digunderground/secura/STL/Secura-stand/Secura Stand-filled.png

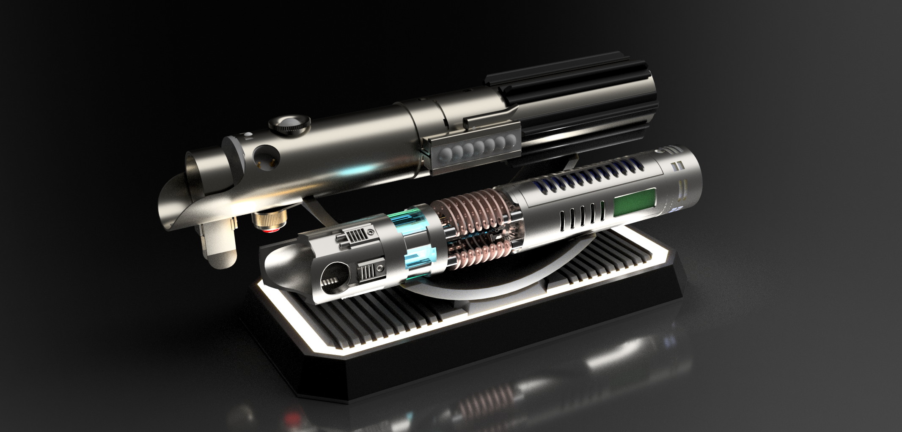
STL/Secura-stand/Secura Stand-filled.png
