digunderground/secura/Extras/proffieTester/STL/wiring_tester_v5_test-bottom.stl

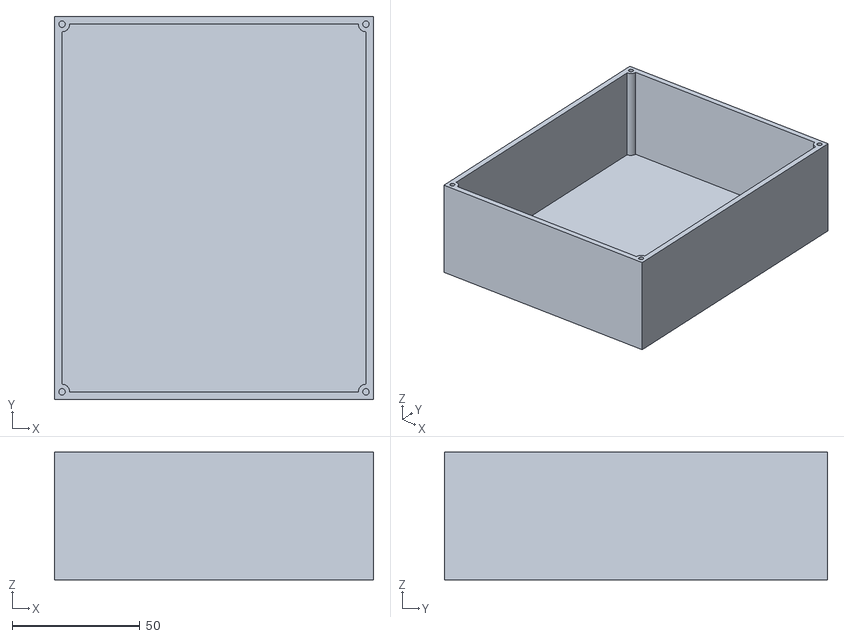
[picture p25: CAD file, 2025-04-27]
Extras/proffieTester/STL/wiring_tester_v5_test-bottom.stl
125.0 x 150.0 x 50.0
