digunderground/secura/MODS/Digunderground/experimental/Secura-chassis/Secura-CH-EXP-21700-Chassis.step

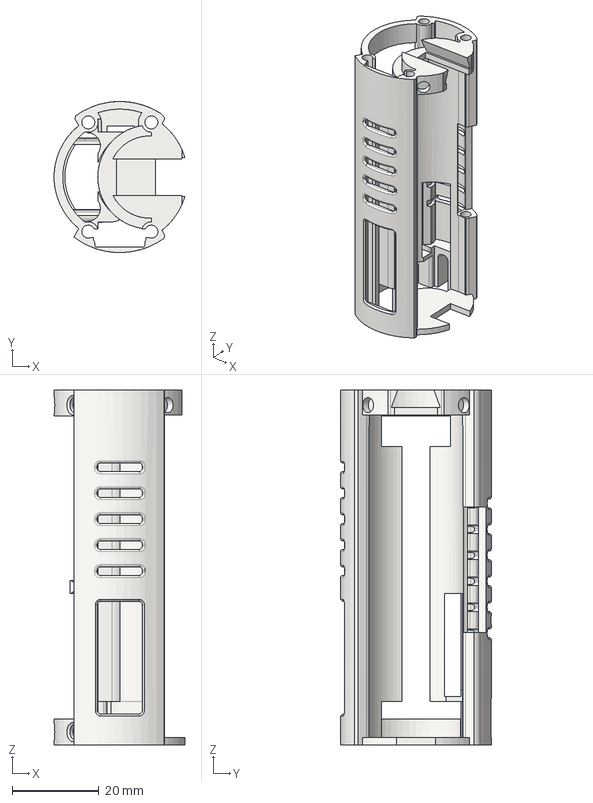
[picture p26: CAD file, 2025-04-13]
MODS/Digunderground/experimental/Secura-chassis/Secura-CH-EXP-21700-Chassis.step
30.2 x 34.9 x 82.0 mm
