digunderground/secura/STL/Secura-chassis/CH-chassis.stl

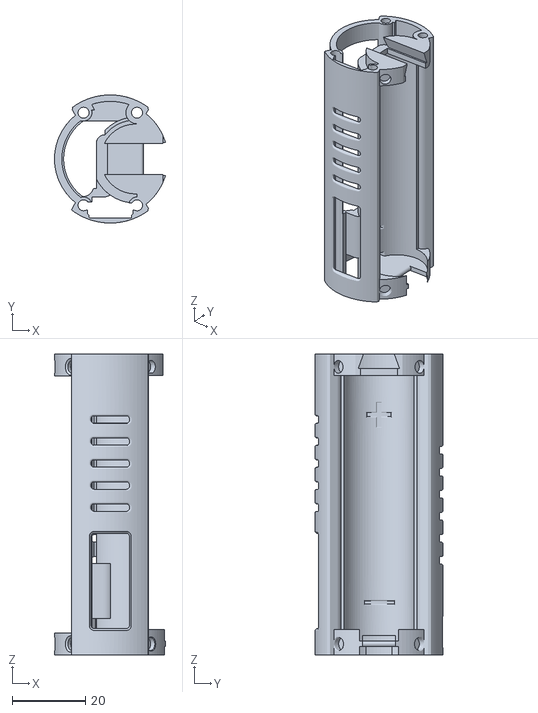
[picture p27: CAD file, 2025-05-18]
STL/Secura-chassis/CH-chassis.stl
30.2 x 34.9 x 82.0
