digunderground/secura/STL/Secura-crystalChamber/SPG-reactor.stl

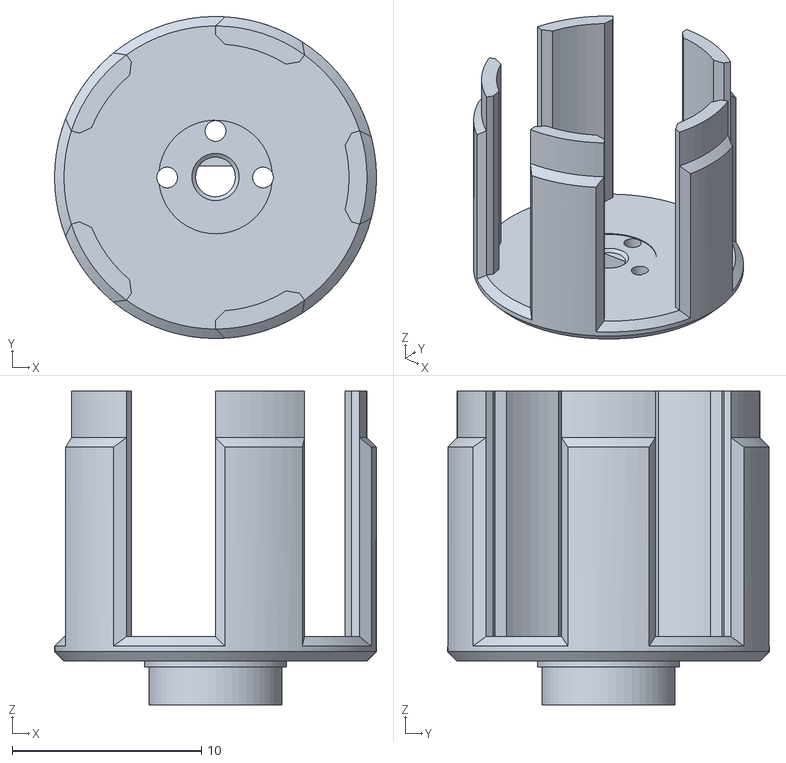
[picture p28: CAD file, 2025-05-18]
STL/Secura-crystalChamber/SPG-reactor.stl
17.0 x 17.0 x 16.6
