digunderground/secura/STL/Secura-emitter/EM-button.stl

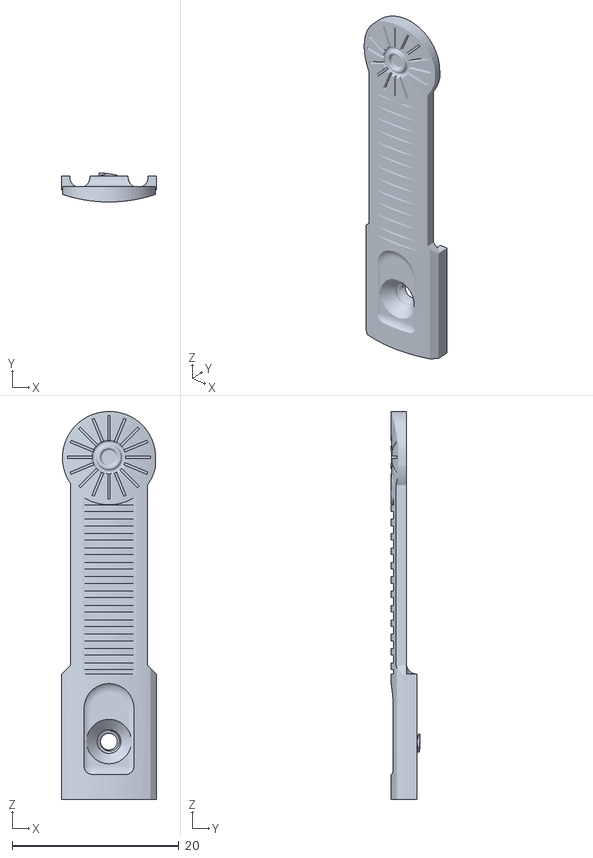
[picture p29: CAD file, 2025-05-18]
STL/Secura-emitter/EM-button.stl
11.4 x 3.48 x 46.6
