digunderground/secura/STL/Secura-speaker/28mm/SP-28mm-holder.stl

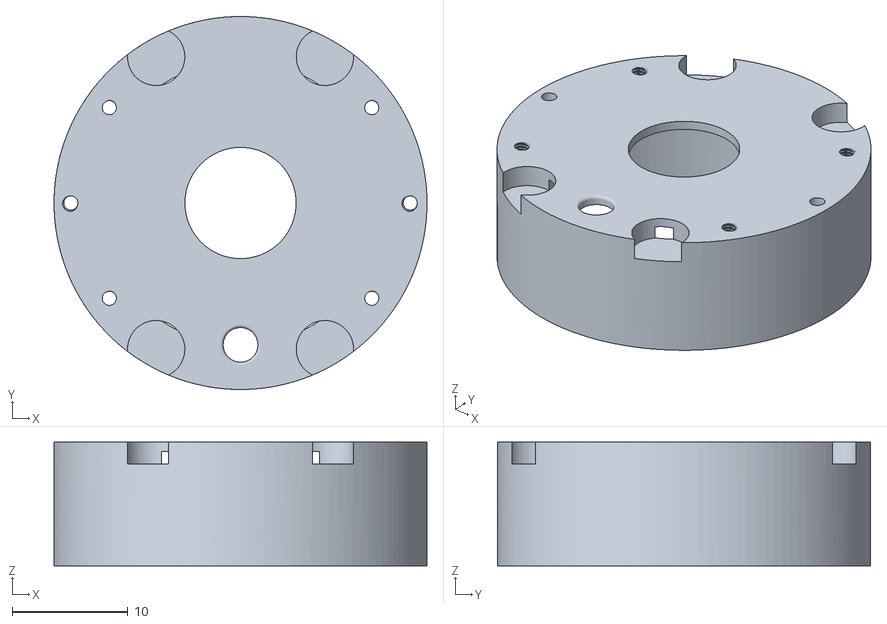
[picture p30: CAD file, 2025-05-18]
STL/Secura-speaker/28mm/SP-28mm-holder.stl
32.2 x 32.2 x 10.7
