digunderground/secura/STL/Secura-speaker/33mm/SP-33mm-outer.stl

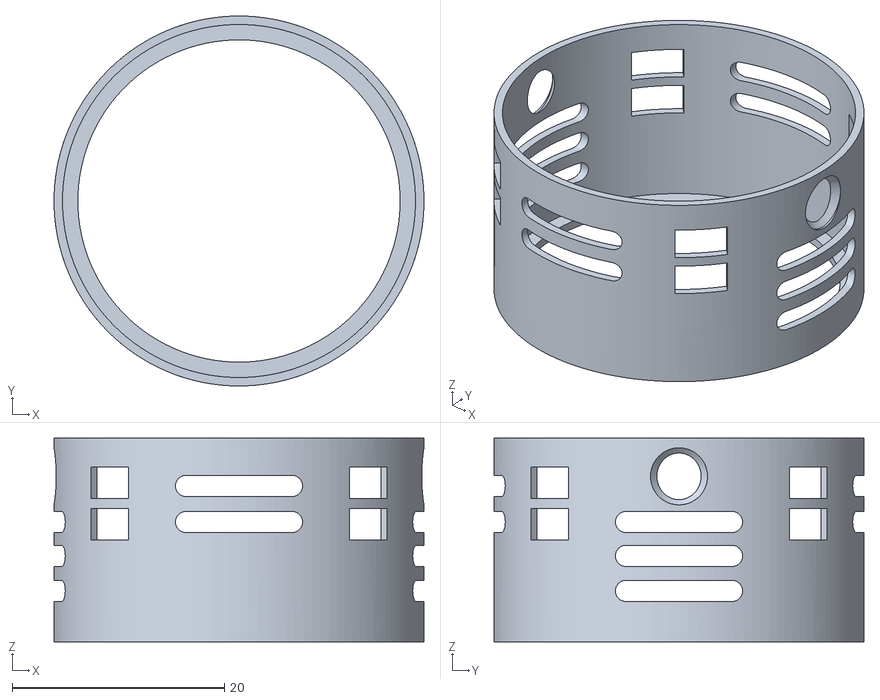
[picture p31: CAD file, 2025-05-18]
STL/Secura-speaker/33mm/SP-33mm-outer.stl
34.9 x 34.9 x 19.2
