digunderground/secura/STL/Secura-stand/SS-outerPlatform.stl

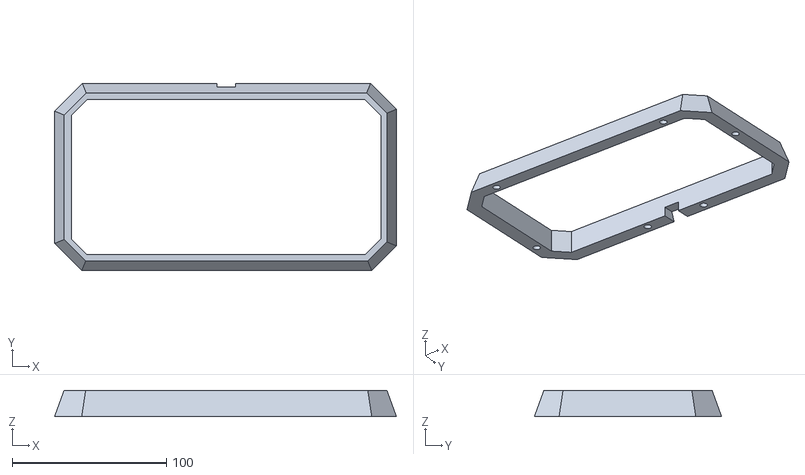
[picture p32: CAD file, 2025-05-17]
STL/Secura-stand/SS-outerPlatform.stl
221.6 x 121.4 x 17.0
