digunderground/secura/CAD/STEP/Secura-CrystalChamber.step

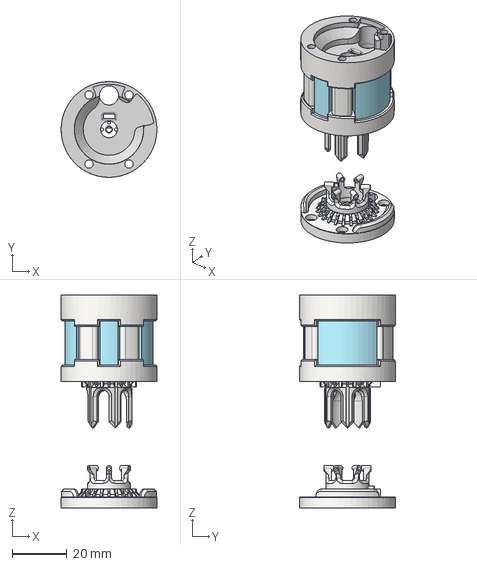
[picture p33: CAD file, 2025-05-18]
CAD/STEP/Secura-CrystalChamber.step
34.9 x 34.9 x 77.6 mm
