digunderground/secura/Extras/proffieTester/STL/wiring_tester_v5_test-top.stl

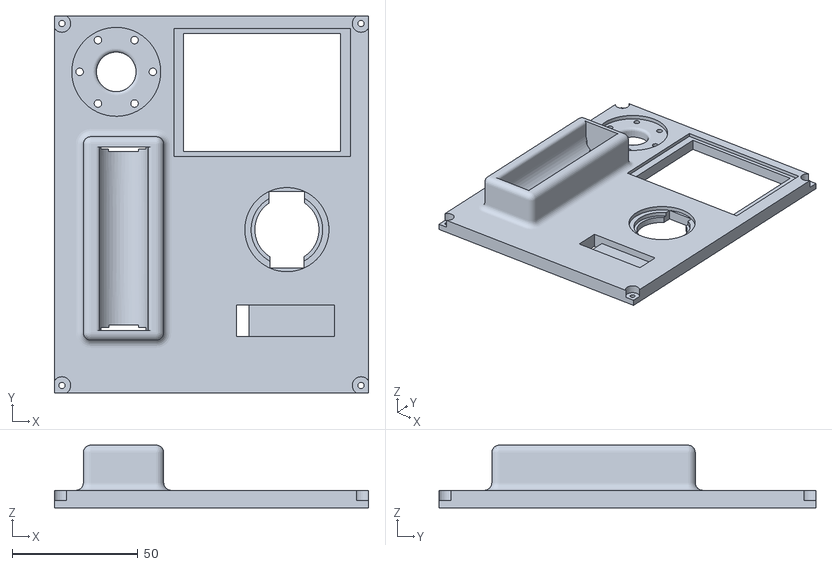
[picture p34: CAD file, 2025-04-27]
Extras/proffieTester/STL/wiring_tester_v5_test-top.stl
125.0 x 150.0 x 25.0
