digunderground/secura/STL/Secura-chassis/CH-ISO_Battery.stl

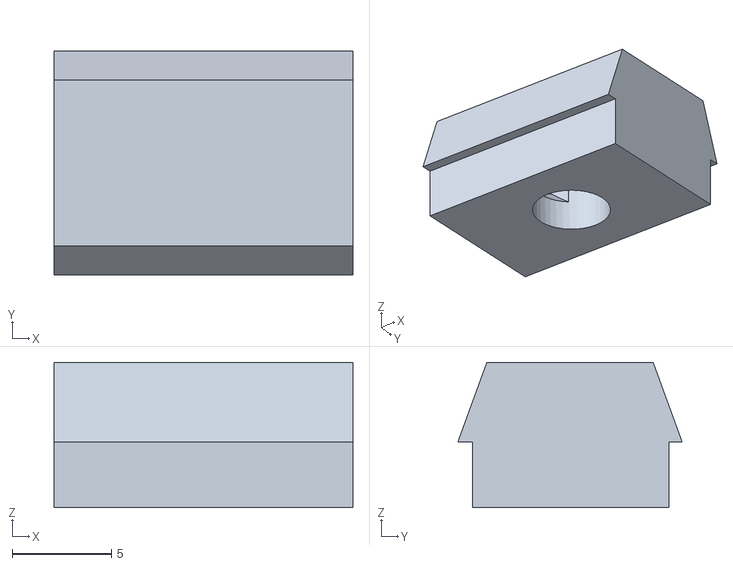
[picture p35: CAD file, 2025-05-18]
STL/Secura-chassis/CH-ISO_Battery.stl
15.1 x 11.3 x 7.30
