digunderground/secura/STL/Secura-crystalChamber/CC-base.stl

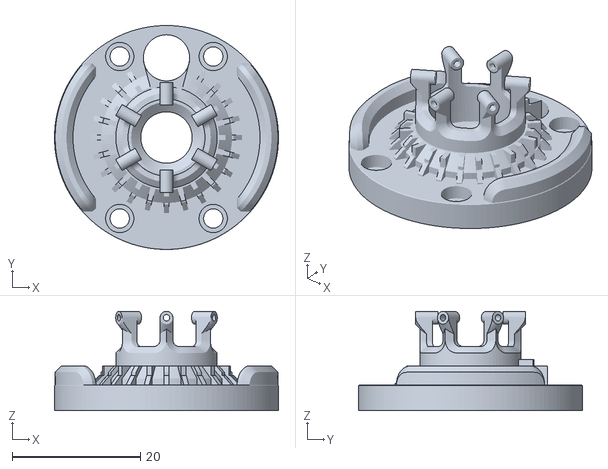
[picture p36: CAD file, 2025-05-18]
STL/Secura-crystalChamber/CC-base.stl
34.9 x 34.9 x 15.5
