digunderground/secura/STL/Secura-crystalChamber/NOP/NOP-CC-coolingFin-single.stl

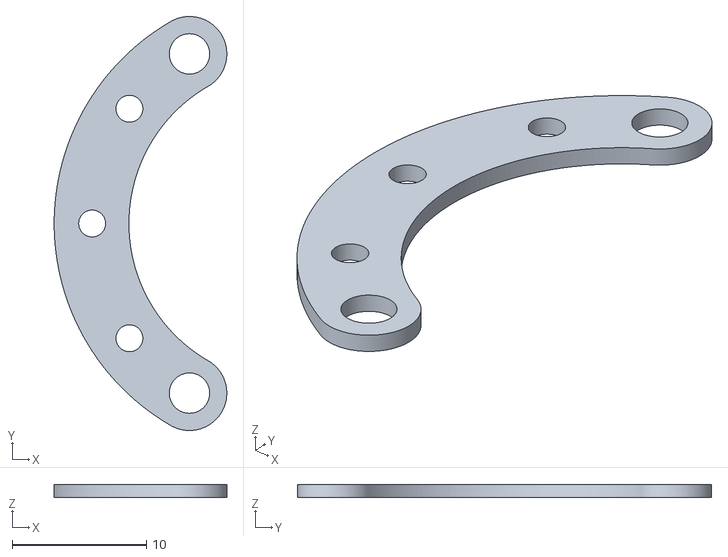
[picture p37: CAD file, 2025-06-01]
STL/Secura-crystalChamber/NOP/NOP-CC-coolingFin-single.stl
12.8 x 30.8 x 1.00
