digunderground/secura/STL/Secura-emitter/EM-top.stl

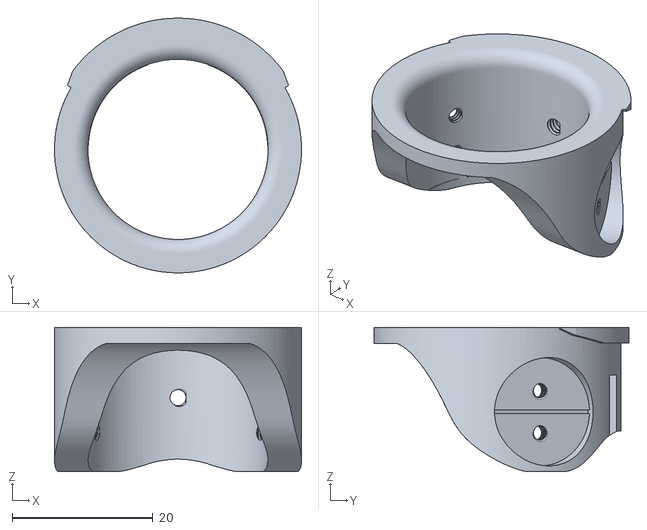
[picture p38: CAD file, 2025-05-18]
STL/Secura-emitter/EM-top.stl
35.1 x 36.2 x 20.5
