digunderground/secura/STL/Secura-stand/SS-hiltHolder.stl

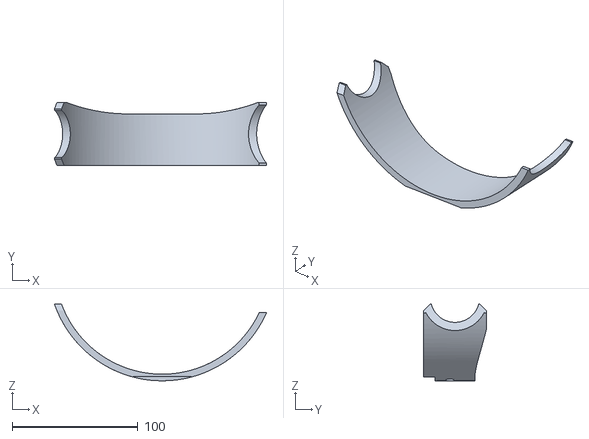
[picture p39: CAD file, 2025-05-17]
STL/Secura-stand/SS-hiltHolder.stl
168.9 x 50.0 x 61.1
