digunderground/secura/Extras/proffieTester/STL/wiring_tester_v5_faux-18650.stl

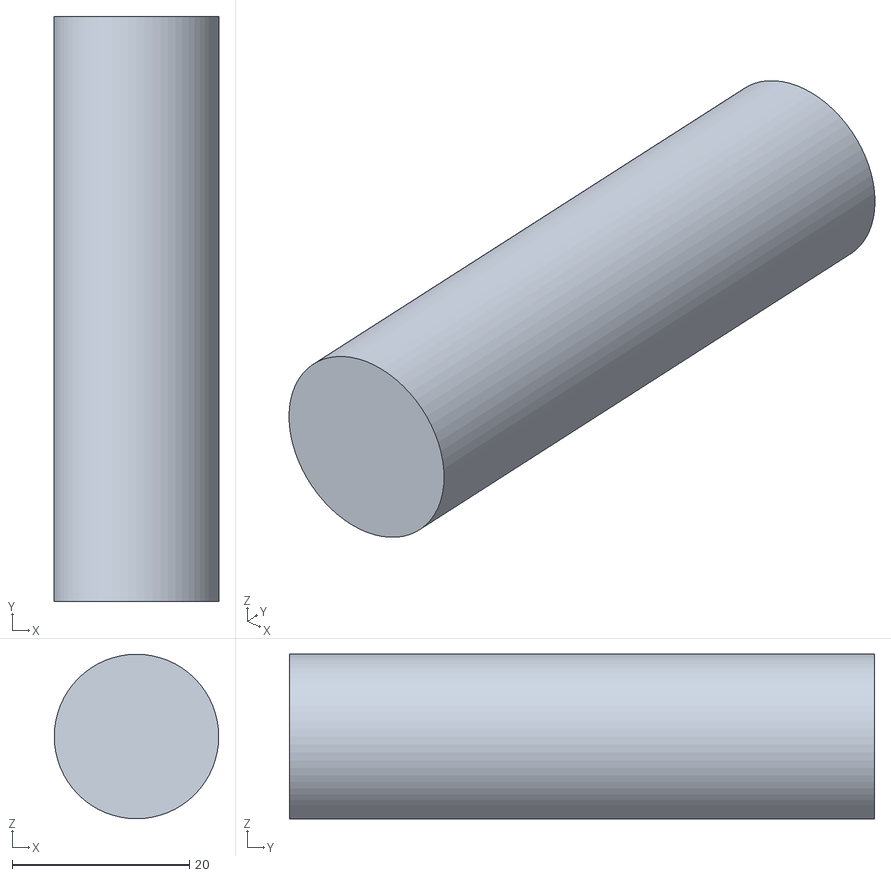
[picture p40: CAD file, 2025-04-27]
Extras/proffieTester/STL/wiring_tester_v5_faux-18650.stl
18.6 x 66.0 x 18.6
