digunderground/secura/STL/Secura-chassis/CH-ISO_screen.stl

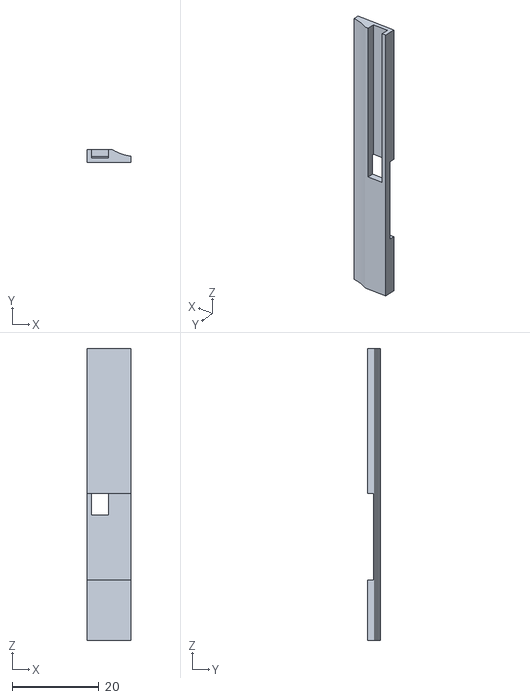
[picture p41: CAD file, 2025-05-18]
STL/Secura-chassis/CH-ISO_screen.stl
10.2 x 2.93 x 67.4
