digunderground/secura/STL/Secura-crystalChamber/SPG-collector.stl

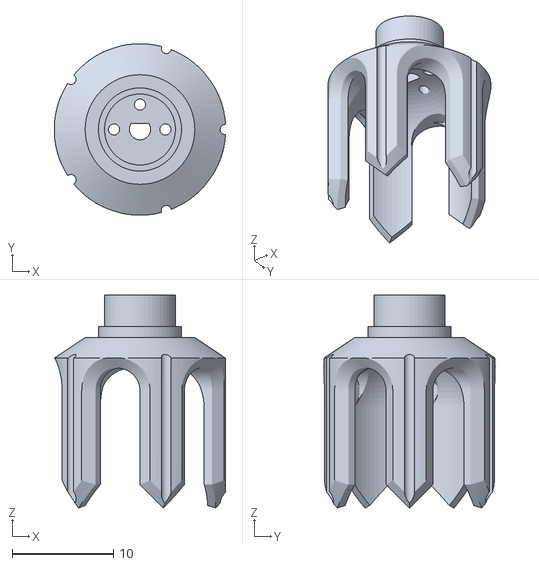
[picture p42: CAD file, 2025-05-18]
STL/Secura-crystalChamber/SPG-collector.stl
16.9 x 16.9 x 21.0
