digunderground/secura/STL/Secura-emitter/EM-base.stl

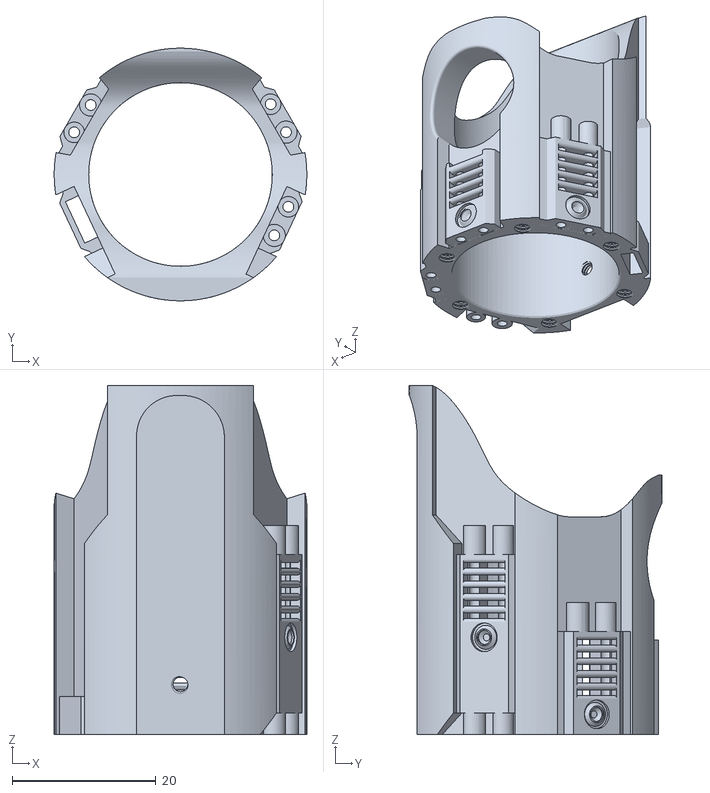
[picture p43: CAD file, 2025-05-18]
STL/Secura-emitter/EM-base.stl
35.1 x 35.1 x 48.5
