digunderground/secura/STL/Secura-stand/SS-chassisHolder.stl

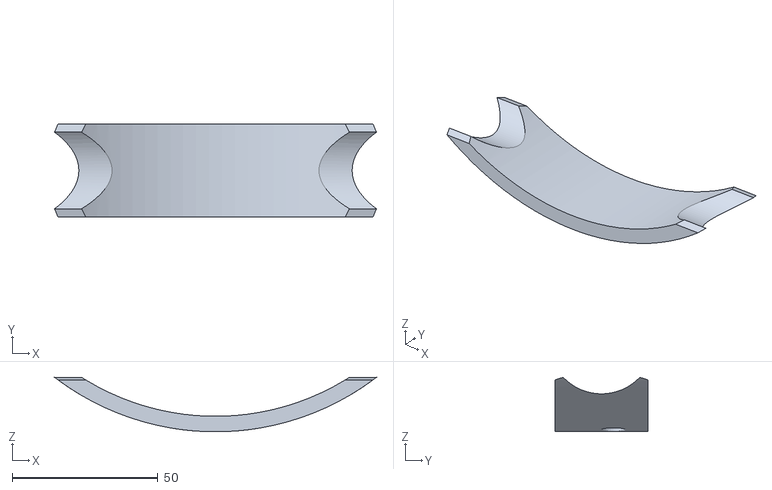
[picture p44: CAD file, 2025-05-17]
STL/Secura-stand/SS-chassisHolder.stl
110.3 x 32.0 x 18.6
