digunderground/secura/STL/Secura-chassis/CH-base.stl

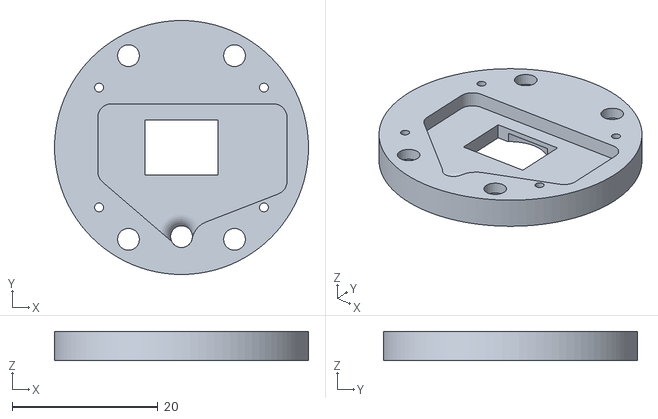
[picture p45: CAD file, 2025-05-18]
STL/Secura-chassis/CH-base.stl
34.9 x 34.9 x 4.00
