digunderground/secura/STL/Secura-crystalChamber/SPG-top.stl

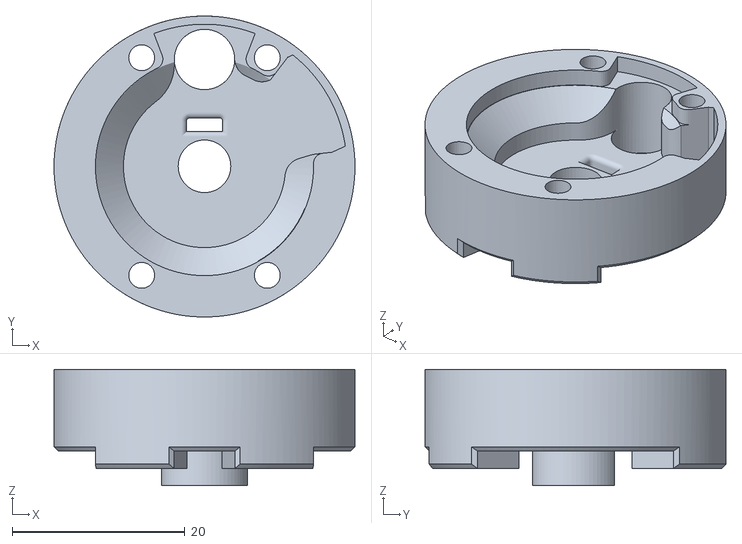
[picture p46: CAD file, 2025-05-18]
STL/Secura-crystalChamber/SPG-top.stl
34.9 x 34.9 x 13.5
