digunderground/secura/STL/Secura-stand/SS-lightDiffuser.stl

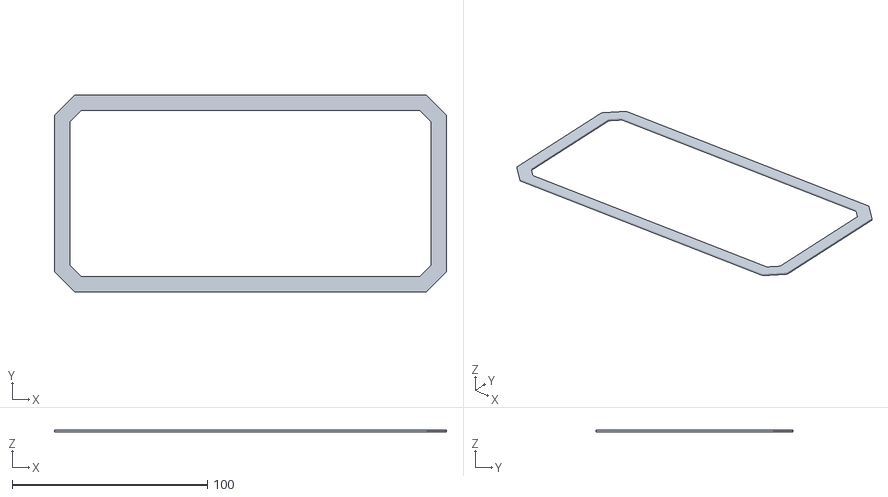
[picture p47: CAD file, 2025-05-17]
STL/Secura-stand/SS-lightDiffuser.stl
200.8 x 100.8 x 1.10
