digunderground/secura/STL/Secura-chassis/CH-electronicsDoor.stl

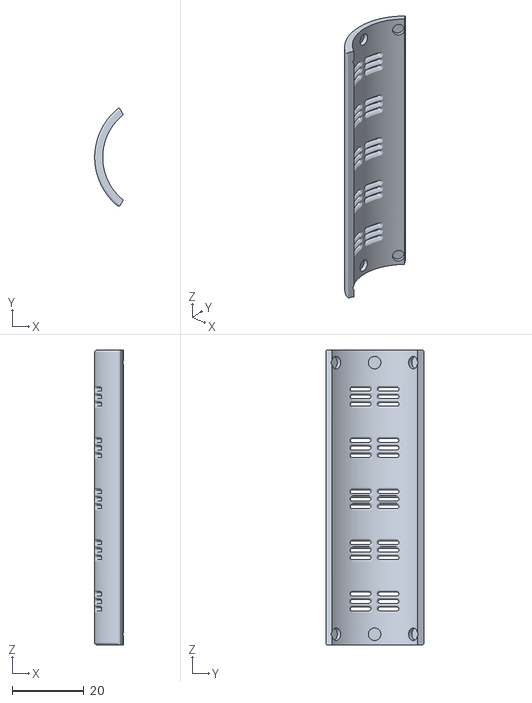
[picture p48: CAD file, 2025-05-18]
STL/Secura-chassis/CH-electronicsDoor.stl
7.97 x 27.2 x 82.0
