digunderground/secura/STL/Secura-crystalChamber/SPG-base.stl

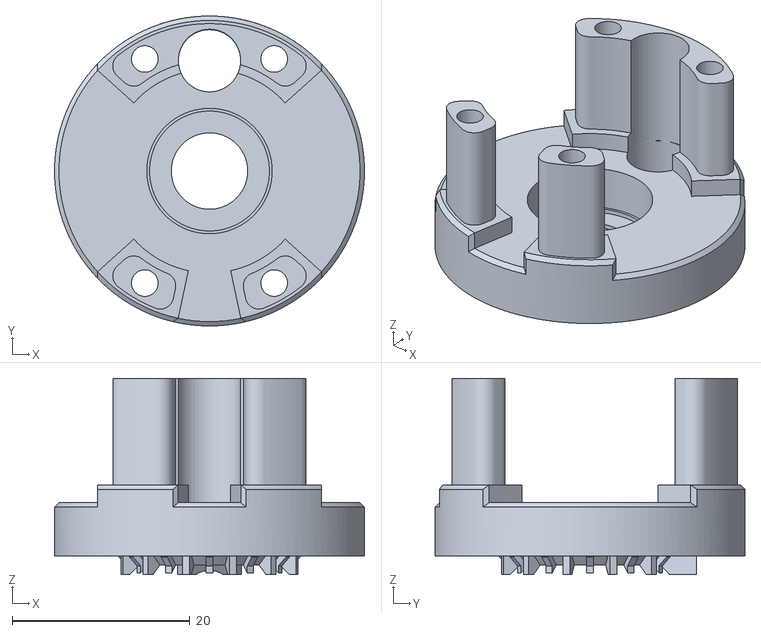
[picture p49: CAD file, 2025-05-18]
STL/Secura-crystalChamber/SPG-base.stl
34.9 x 34.9 x 22.1
