digunderground/secura/STL/Secura-stand/SS-base.stl

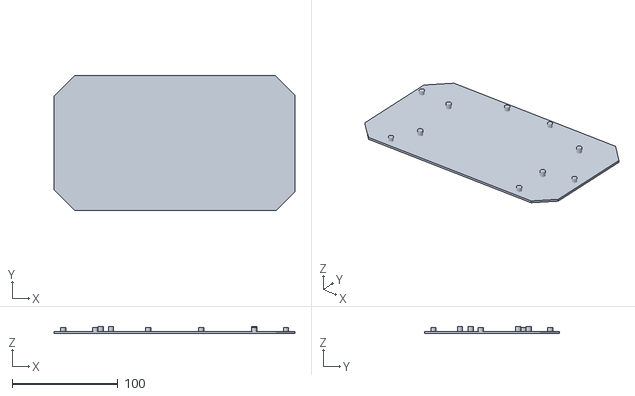
[picture p50: CAD file, 2025-05-17]
STL/Secura-stand/SS-base.stl
227.6 x 127.4 x 7.00
