digunderground/secura/STL/Secura-chassis/CH-batteryTerminal.stl

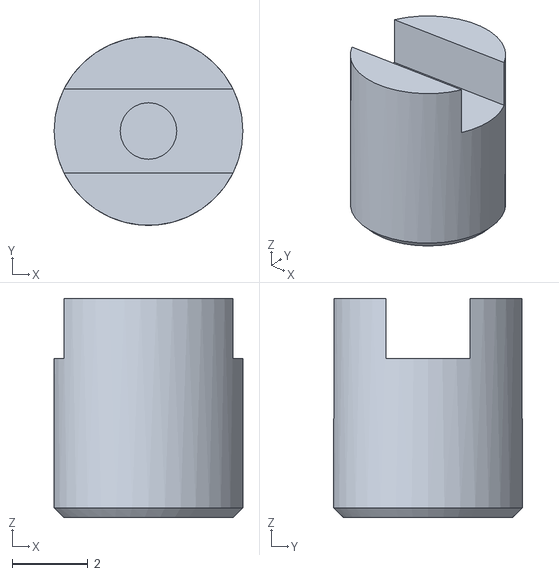
[picture p51: CAD file, 2025-05-18]
STL/Secura-chassis/CH-batteryTerminal.stl
5.00 x 5.00 x 5.80
