digunderground/secura/STL/Secura-stand/SS-deck.stl

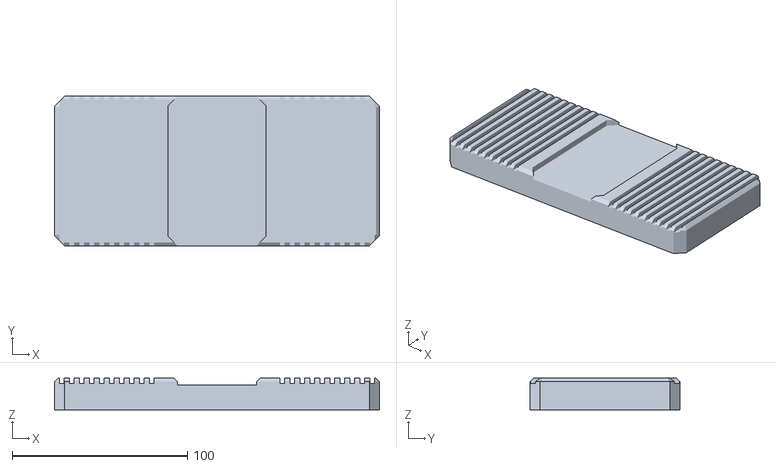
[picture p52: CAD file, 2025-05-17]
STL/Secura-stand/SS-deck.stl
185.4 x 85.4 x 18.0
