digunderground/secura/STL/Secura-chassis/CH-batteryDoor.stl

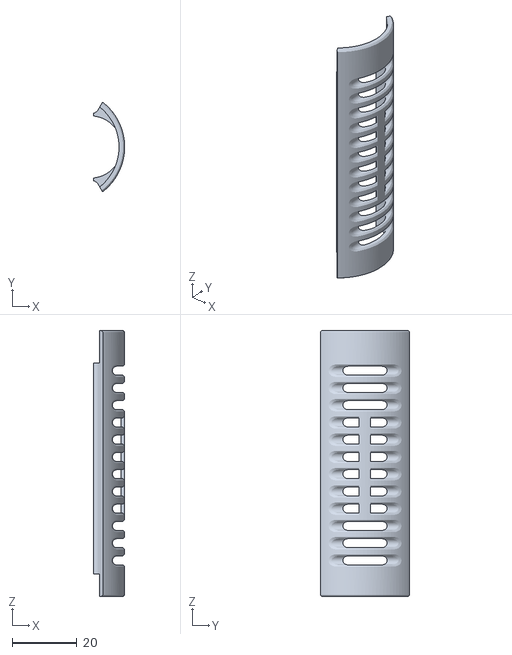
[picture p53: CAD file, 2025-05-18]
STL/Secura-chassis/CH-batteryDoor.stl
9.67 x 27.4 x 82.0
