digunderground/secura/STL/Secura-chassis/CH-ISO_Proffie.stl

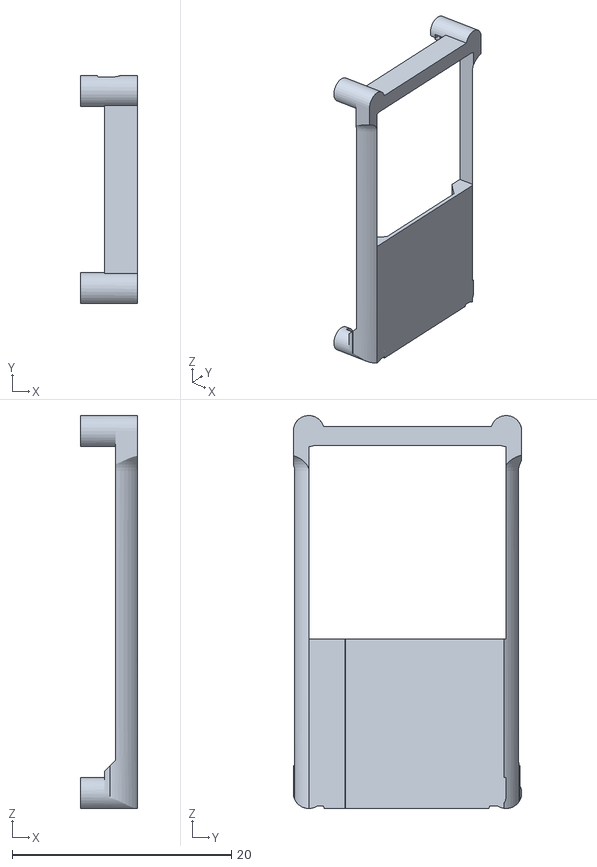
[picture p54: CAD file, 2025-05-18]
STL/Secura-chassis/CH-ISO_Proffie.stl
5.20 x 20.8 x 35.8
